supercow/photon_clock/enclosure/Renderings/assembled_side-angle.png

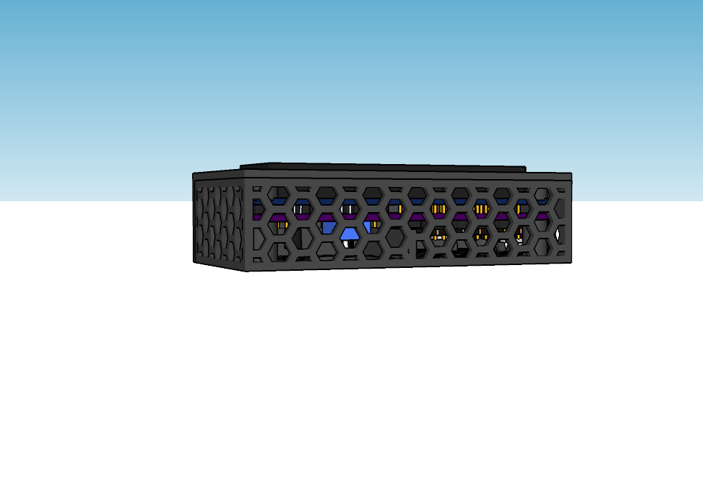
enclosure/Renderings/assembled_side-angle.png
