supercow/photon_clock/enclosure/Renderings/assembled_top-view.png

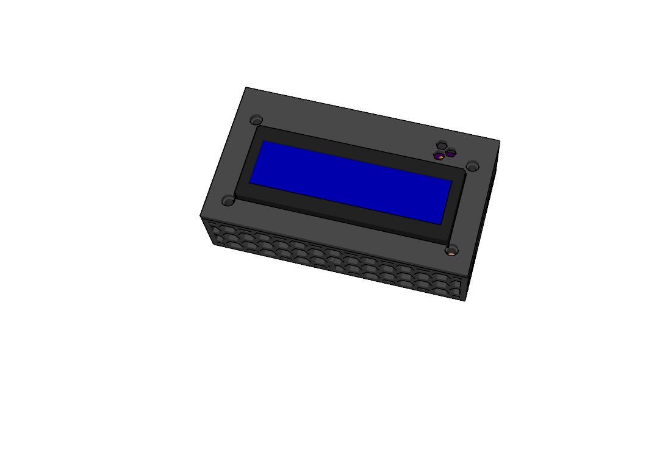
enclosure/Renderings/assembled_top-view.png
